re-innovation/RenewableRegulator/PCB/RenewableRegulatorPCB_2017/FETControl.sch

## KiCad design PCB/RenewableRegulatorPCB_2017/FETControl.sch (2017-04-10, an earlier design)

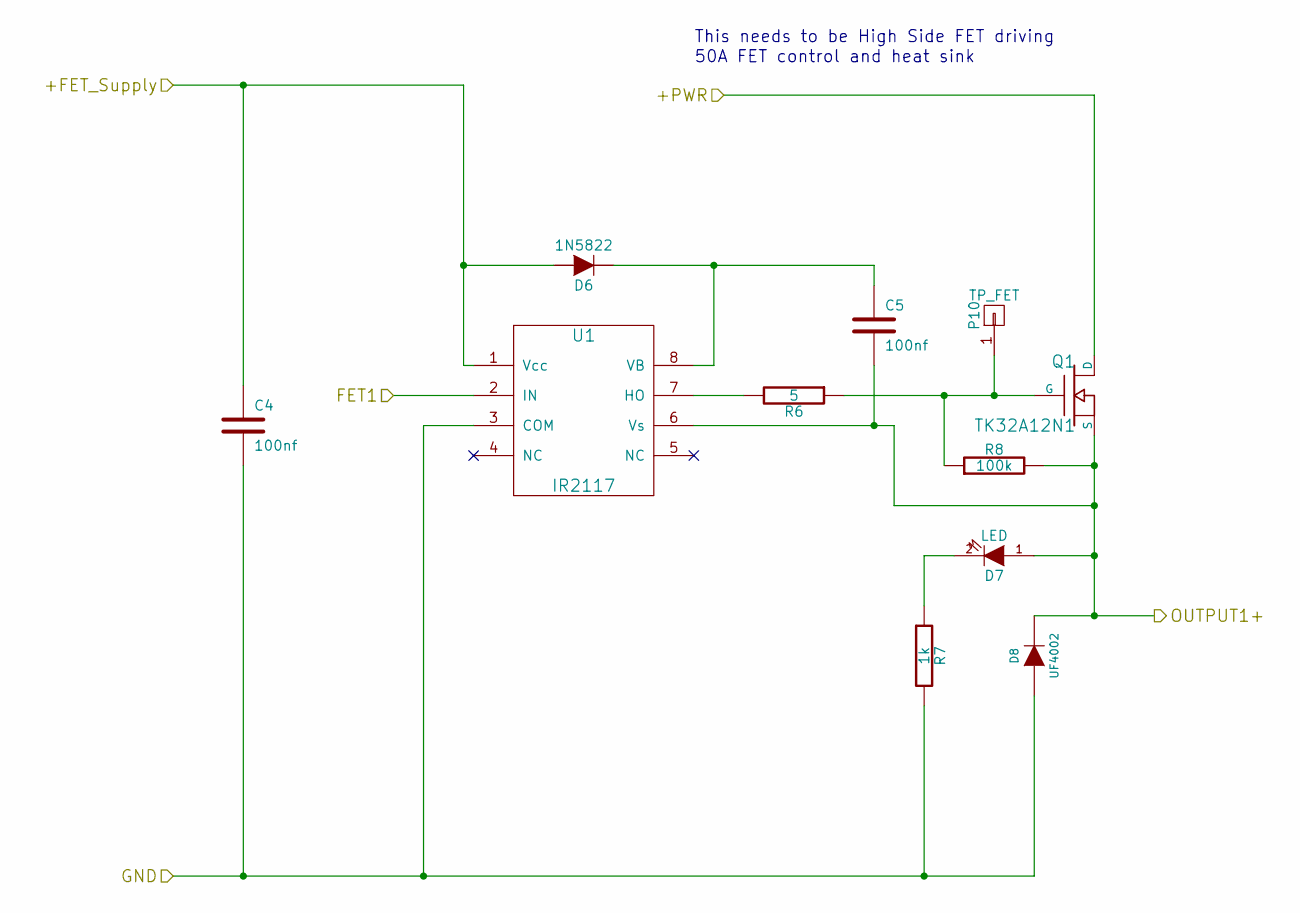
[picture p48: schematic FETControl.sch]

Parts:
C4, C5: 100nf; C1_wide_lg_pad
D6: 1N5822; TH_Diode_1; Manufacturer Part No 1N5822
D7: LED; TH_LED-5MM_larg_pad
D8: UF4002; TH_Diode_1; Manufacturer Part No UF4002-E3
P10: TP_FET; 1pin_0_8mm
Q1: TK32A12N1; TO220_VERT_BUZ11_matt; Manufacturer Part No TK32A12N1,S4X
R6: 5; TH_Resistor_1
R7: 1k; TH_Resistor_1
R8: 100k; TH_Resistor_1
U1: IR2117; DIP-8_300_ELL; Manufacturer Part No IR2117PBF

Connections:
+FET_Supply: C4.1, D6.2 (A), U1.1 (Vcc)
+PWR: Q1.D
FET1: U1.2 (IN)
GND: C4.2, D8.2 (A), R7.2, U1.3 (COM)
unnamed: C5.1, D6.1 (K), U1.8 (VB)
unnamed: D7.2 (K), R7.1
unnamed: P10.1, Q1.G, R6.1, R8.1
unnamed: R6.2, U1.7 (HO)
OUTPUT1+: C5.2, D7.1 (A), D8.1 (K), Q1.S, R8.2, U1.6 (Vs)

Notes on the sheet:
This needs to be High Side FET driving
50A FET control and heat sink
