re-innovation/RenewableRegulator/PCB/RenewableRegulatorPCB_2017/powersupply.sch

## KiCad design PCB/RenewableRegulatorPCB_2017/powersupply.sch (2017-05-31, an earlier design)

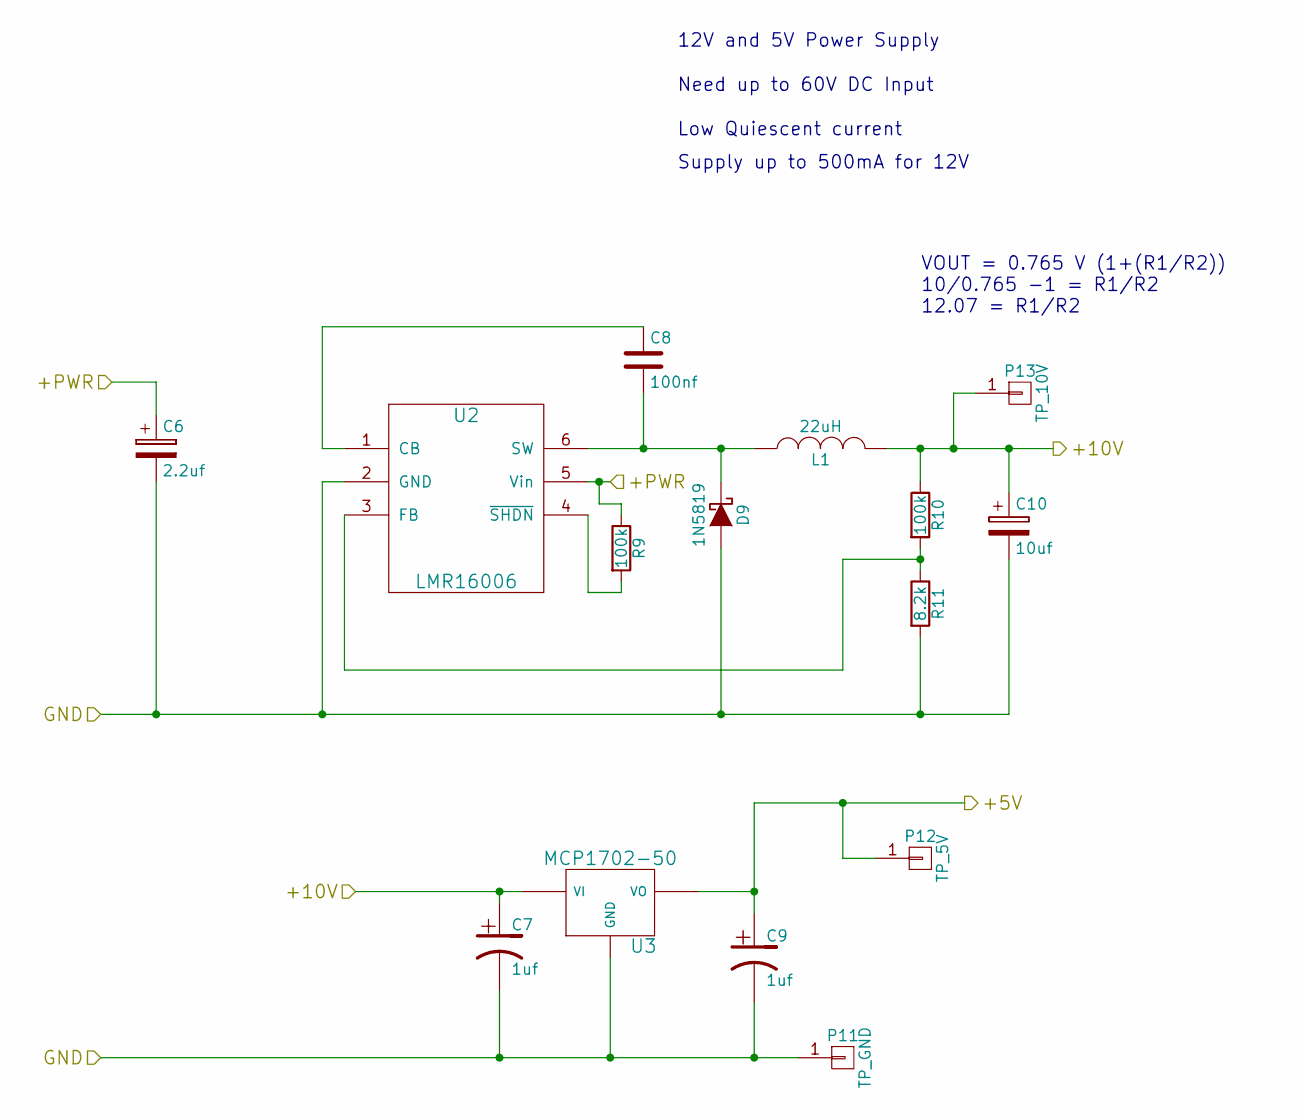
[picture p50: schematic powersupply.sch]

Parts:
C6: 2.2uf; Capacitor_C6_1V7_TH; Manufacturer Part No RDEC72A225K3M1H03A
C7: 1uf; Capacitor_C7_1V7_TH; Manufacturer Part No RCER71H105K2M1H03A
C8: 100nf; C1_wide_lg_pad
C9: 1uf; Capacitor_C9_1V7_TH; Manufacturer Part No RCER71H105K2M1H03A
C10: 10uf; Capacitor_C10_1V7_TH; Manufacturer Part No EEUFR1H100
D9: 1N5819; TH_Diode_1; Manufacturer Part No 1N5819
L1: 22uH; TH_Inductor; Manufacturer Part No 744772220
P11: TP_GND; 1pin_0_8mm
P12: TP_5V; 1pin_0_8mm
P13: TP_10V; 1pin_0_8mm
R9, R10: 100k; TH_Resistor_1
R11: 8.2k; TH_Resistor_1
U2: LMR16006; SM_SOT23-6; Manufacturer Part No LMR16006YDDCT
U3: MCP1702-50; TO92_MCP9701_matt; Manufacturer Part No MCP1702-5002E/TO

Connections:
+5V: C9.1, P12.1, U3.VO
+10V: C7.1, C10.1, L1.2, P13.1, R10.1, U3.VI
+PWR: C6.1, R9.1, U2.5 (Vin)
GND: C6.2, C7.2, C9.2, C10.2, D9.2 (A), P11.1, R11.2, U2.2 (GND), U3.GND
unnamed: C8.1, U2.1 (CB)
unnamed: C8.2, D9.1 (K), L1.1, U2.6 (SW)
unnamed: R9.2, U2.4 (~SHDN)
unnamed: R10.2, R11.1, U2.3 (FB)

Notes on the sheet:
12V and 5V Power Supply
Need up to 60V DC Input
Low Quiescent current
Supply up to 500mA for 12V
VOUT = 0.765 V (1+(R1/R2)) 10/0.765 -1 = R1/R2 12.07 = R1/R2
