re-innovation/RenewableRegulator/PCB/RenewableRegulator_MPPT_PCB_2017/BUCK converter.sch

## KiCad design PCB/RenewableRegulator_MPPT_PCB_2017/BUCK converter.sch (2017-05-05, an earlier design)

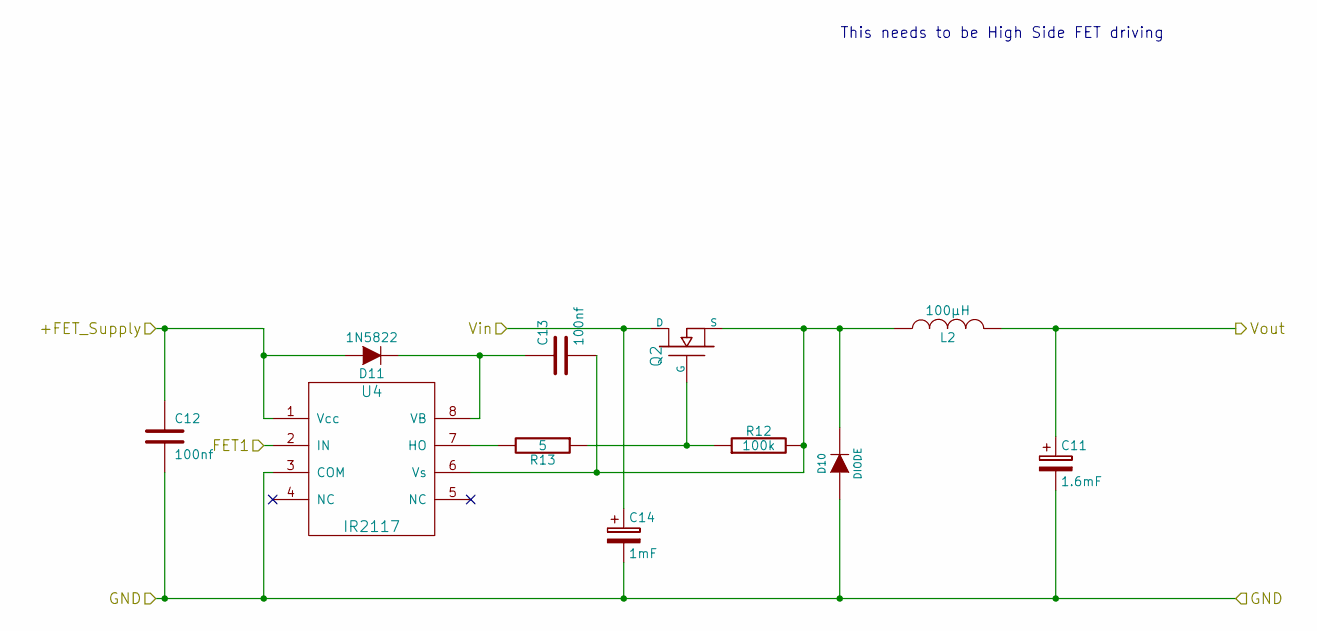
[picture p51: schematic BUCK converter.sch]

Parts:
C11: 1.6mF; Capacitor_C_1V7_TH; Manufacturer Part No ECA-2AM101B
C12, C13: 100nf; C1_wide_lg_pad
C14: 1mF; Capacitor_C_1V7_TH; Manufacturer Part No ECA-2AM101B
D10: DIODE
D11: 1N5822; TH_Diode_1; Manufacturer Part No 1N5822
L2: 100µH
Q2: TK32A12N1; TO220_VERT_BUZ11_matt; Manufacturer Part No TK32A12N1,S4X
R12: 100k; TH_Resistor_1
R13: 5; TH_Resistor_1
U4: IR2117; DIP-8_300_ELL; Manufacturer Part No IR2117PBF

Connections:
+FET_Supply: C12.1, D11.2 (A), U4.1 (Vcc)
FET1: U4.2 (IN)
GND: C11.2, C12.2, C14.2, D10.2 (A), U4.3 (COM)
unnamed: C13.1, D11.1 (K), U4.8 (VB)
unnamed: C13.2, D10.1 (K), L2.1, Q2.S, R12.2, U4.6 (Vs)
unnamed: Q2.G, R12.1, R13.1
unnamed: R13.2, U4.7 (HO)
Vin: C14.1, Q2.D
Vout: C11.1, L2.2

Notes on the sheet:
This needs to be High Side FET driving
