re-innovation/RenewableRegulator/PCB/RenewableRegulator_MPPT_PCB_2017/currentMeasurment.sch

## KiCad design PCB/RenewableRegulator_MPPT_PCB_2017/currentMeasurment.sch (2017-05-19, an earlier design)

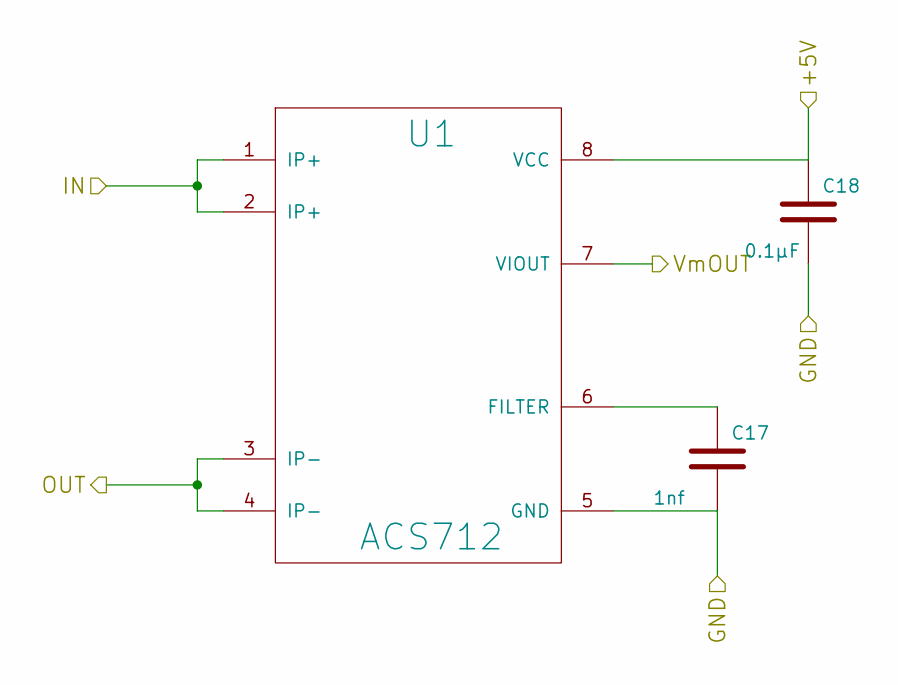
[picture p53: schematic currentMeasurment.sch]

Parts:
C15: 1nf; C1_wide_lg_pad
C16: 0.1µF; C1_wide_lg_pad
U5: ACS712

Connections:
+5V: C16.1, U5.8 (VCC)
GND: C15.2, C16.2, U5.5 (GND)
IN: U5.1 (IP+), U5.2 (IP+)
unnamed: C15.1, U5.6 (FILTER)
OUT: U5.3 (IP-), U5.4 (IP-)
VmOUT: U5.7 (VIOUT)
